gogomaker/HangeulClock_DIY_v2/testCode/RTCtest/RTCtest.ino

#include <Wire.h>
#define DS3231_I2C_ADDRESS 104
// 데이터핀 연결
// SCL - pin A5
// SDA - pin A4
byte seconds, minutes, hours, day, date, month, year;
char weekDay[4];
byte tMSB, tLSB;
float temp3231;

void setup() {
  Wire.begin();
  Serial.begin(9600);
}

void loop() {
  watchConsole();
  get3231Date();

  Serial.print(weekDay);
  Serial.print(", 20");
  Serial.print(year, DEC);
  Serial.print("/");
  Serial.print(month, DEC);
  Serial.print("/");
  Serial.print(date, DEC);
  Serial.print(" - ");
  Serial.print(hours, DEC); 
  Serial.print(":"); 
  Serial.print(minutes, DEC); 
  Serial.print(":"); 
  Serial.print(seconds, DEC);
  Serial.print(" - Temp: "); 
  Serial.println(get3231Temp());
  delay(1000);
}

// 10진수를 2진화 10진수인 BCD 로 변환 (Binary Coded Decimal)
byte decToBcd(byte val) {
  return ((val/10*16)+(val%10));
}

void watchConsole() {
  if (Serial.available()) {      // Look for char in serial queue and process if found
    if (Serial.read() == 84) {   //If command = "T" Set Date
      set3231Date();
      get3231Date();
      Serial.println(" ");
    }
  }
}

//시간설정
// T(설정명령) + 년(00~99) + 월(01~12) + 일(01~31) + 시(00~23) + 분(00~59) + 초(00~59) + 요일(1~7, 일1 월2 화3 수4 목5 금6 토7)
// 예: T1605091300002 (2016년 5월 9일 13시 00분 00초 월요일)
void set3231Date()
{
  year    = (byte) ((Serial.read() - 48) *10 +  (Serial.read() - 48));
  month   = (byte) ((Serial.read() - 48) *10 +  (Serial.read() - 48));
  date    = (byte) ((Serial.read() - 48) *10 +  (Serial.read() - 48));
  hours   = (byte) ((Serial.read() - 48) *10 +  (Serial.read() - 48));
  minutes = (byte) ((Serial.read() - 48) *10 +  (Serial.read() - 48));
  seconds = (byte) ((Serial.read() - 48) * 10 + (Serial.read() - 48));
  day     = (byte) (Serial.read() - 48);

  Wire.beginTransmission(DS3231_I2C_ADDRESS);
  Wire.write(0x00);
  Wire.write(decToBcd(seconds));
  Wire.write(decToBcd(minutes));
  Wire.write(decToBcd(hours));
  Wire.write(decToBcd(day));
  Wire.write(decToBcd(date));
  Wire.write(decToBcd(month));
  Wire.write(decToBcd(year));
  Wire.endTransmission();
} 

void get3231Date()
{
  // send request to receive data starting at register 0
  Wire.beginTransmission(DS3231_I2C_ADDRESS); // 104 is DS3231 device address
  Wire.write(0x00); // start at register 0
  Wire.endTransmission();
  Wire.requestFrom(DS3231_I2C_ADDRESS, 7); // request seven bytes

  if(Wire.available()) {
    seconds = Wire.read(); // get seconds
    minutes = Wire.read(); // get minutes
    hours   = Wire.read();   // get hours
    day     = Wire.read();
    date    = Wire.read();
    month   = Wire.read(); //temp month
    year    = Wire.read();
    seconds = (((seconds & B11110000)>>4)*10 + (seconds & B00001111)); // convert BCD to decimal
    minutes = (((minutes & B11110000)>>4)*10 + (minutes & B00001111)); // convert BCD to decimal
    hours   = (((hours & B00110000)>>4)*10 + (hours & B00001111)); // convert BCD to decimal (assume 24 hour mode)
    day     = (day & B00000111); // 1-7
    date    = (((date & B00110000)>>4)*10 + (date & B00001111)); // 1-31
    month   = (((month & B00010000)>>4)*10 + (month & B00001111)); //msb7 is century overflow
    year    = (((year & B11110000)>>4)*10 + (year & B00001111));
  }
  else {
    //oh noes, no data!
  }

  switch (day) {
    case 1:
      strcpy(weekDay, "Sun");
      break;
    case 2:
      strcpy(weekDay, "Mon");
      break;
    case 3:
      strcpy(weekDay, "Tue");
      break;
    case 4:
      strcpy(weekDay, "Wed");
      break;
    case 5:
      strcpy(weekDay, "Thu");
      break;
    case 6:
      strcpy(weekDay, "Fri");
      break;
    case 7:
      strcpy(weekDay, "Sat");
      break;
  }
}

float get3231Temp()
{
  //temp registers (11h-12h) get updated automatically every 64s
  Wire.beginTransmission(DS3231_I2C_ADDRESS);
  Wire.write(0x11);
  Wire.endTransmission();
  Wire.requestFrom(DS3231_I2C_ADDRESS, 2);

  if(Wire.available()) {
    tMSB = Wire.read(); //2's complement int portion
    tLSB = Wire.read(); //fraction portion
    temp3231 = (tMSB & B01111111); //do 2's math on Tmsb
    temp3231 += ( (tLSB >> 6) * 0.25 ); //only care about bits 7 & 8
  }
  else {
    //error.
  }
  return temp3231;
}
